kylecmathias/FlipperInfinity/ui/assets/IR.png

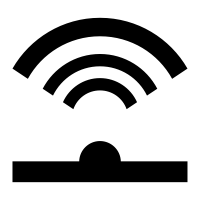
ui/assets/IR.png
