kylecmathias/FlipperInfinity/ui/assets/NO WIFI.png

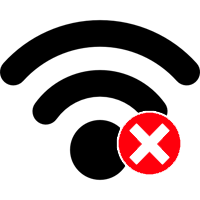
ui/assets/NO WIFI.png
