kylecmathias/FlipperInfinity/ui/assets/RF.png

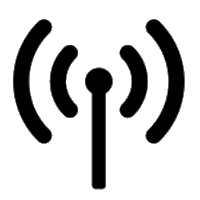
ui/assets/RF.png
