kylecmathias/FlipperInfinity/include/ir_menu.hpp

#pragma once

#include "header.hpp"
#include "ui_bridge.hpp"

inline constexpr uint32_t IR_RES_HZ = 1000000;
inline constexpr uint32_t IR_TX_CARRIER_FREQ_HZ = 38000;
inline constexpr float IR_TX_CARRIER_DUTY = 0.33f;
inline constexpr uint16_t IR_SYMBOL_BUFFER_SIZE = 512;
