kylecmathias/FlipperInfinity/src/ui/images.c

#include "images.h"

const ext_img_desc_t images[10] = {
    { "BLUETOOTH", &img_bluetooth },
    { "IR", &img_ir },
    { "LOGO", &img_logo },
    { "NFC", &img_nfc },
    { "NO BLUETOOTH", &img_no_bluetooth },
    { "NO WIFI", &img_no_wifi },
    { "RF", &img_rf },
    { "RFID", &img_rfid },
    { "settings", &img_settings },
    { "WIFI", &img_wifi },
};
